achmed20/GaragePack/doc/p2.jpg

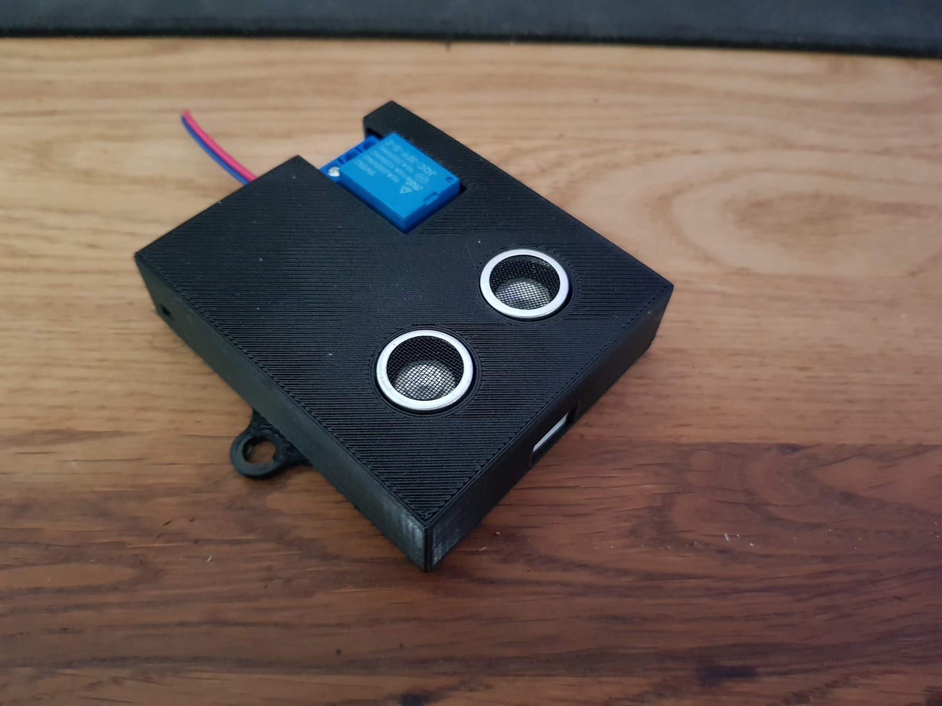
doc/p2.jpg
